shiqi-614/bluetooth_ergodone_doc/pic/leds.jpg

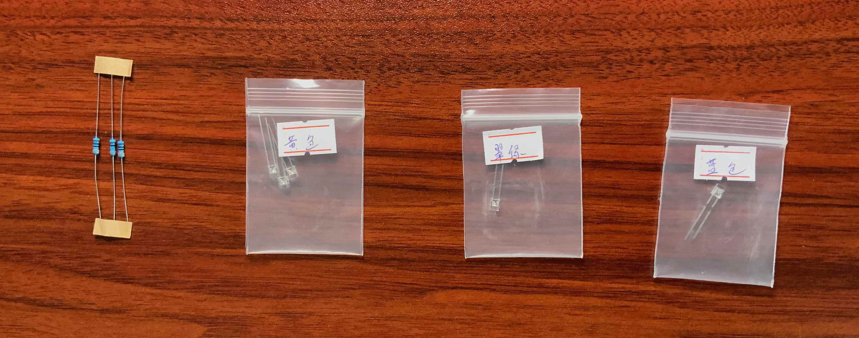
pic/leds.jpg
